KubaO/T-M-Reverse-Engineering/Power Designs 3240/PD3240.cir

[Main]
FileType=CIR
Version=12.00
Program=Micro-Cap
Component Version=10.00
Shape Version=11.00
Screen=1707,960
MCAPVersion=12.2.0.5
Key ID=Demo
NLCnt=299
TXCnt=4

[shapedef]
Name=Animated Meter
Animated Meter=0,-16,128,96
BColor=#000000
FColor=#E4E4E4
Current=-16,64,0,64

[shapedef]
Name=Bjt.root
Line=0,0,13,0
Rectangle=13,-12,15,12
Current=32,-24,32,-16
Current=32,24,32,16
Current=0,-8,8,-8
PolyOpen=3
PolyLine=24,-24
PolyLine=24,-12
PolyLine=14,-2
PolyOpen=3
PolyLine=24,24
PolyLine=24,12
PolyLine=14,2

[shapedef]
Name=Capacitor
Line=0,0,22,0
Line=22,-8,22,8
Line=26,-8,26,8
Line=26,0,48,0
Current=32,12,16,12

[shapedef]
Name=Diode
Root="Diode.root",0,0,0

[shapedef]
Name=Diode.root
Line=0,0,20,0
Line=28,0,48,0
Rectangle=18,-8,20,8
PolyClosed=3
PolyLine=20,0
PolyLine=28,-8
PolyLine=28,8
Current=32,16,16,16

[shapedef]
Name=Ground
Line=0,0,12,0
Line=12,-8,12,8
Line=18,-4,18,4
Line=24,0,24,0

[shapedef]
Name=NPN
Root="Bjt.root",0,0,0
PolyClosed=3
PolyLine=20,12
PolyLine=24,12
PolyLine=24,8

[shapedef]
Name=Plus.root
Line=-2,0,2,0
Line=0,-2,0,2

[shapedef]
Name=PNP
Root="Bjt.root",0,0,0
PolyClosed=3
PolyLine=17,-5
PolyLine=21,-5
PolyLine=17,-9
Line=16,-4,14,-2
Line=16,4,14,2

[shapedef]
Name=Pot
Line=0,0,12,0
Line=12,0,14,-4
Line=14,-4,18,4
Line=18,4,22,-4
Line=22,-4,26,4
Line=26,4,30,-4
Line=30,-4,34,4
Line=34,4,36,0
Line=36,0,48,0
PolyClosed=4
PolyLine=24,4
PolyLine=24,4
PolyLine=22,8
PolyLine=26,8
Line=24,8,24,16

[shapedef]
Name=Resistor
PolyOpen=12
PolyLine=0,0
PolyLine=0,0
PolyLine=12,0
PolyLine=14,-4
PolyLine=18,4
PolyLine=22,-4
PolyLine=26,4
PolyLine=30,-4
PolyLine=34,4
PolyLine=36,0
PolyLine=48,0
PolyLine=48,0
Current=32,8,16,8

[shapedef]
Name=SPICE_V
Root="Vsource.root",0,0,0

[shapedef]
Name=Vsource.root
Line=0,0,12,0
Line=36,0,48,0
Ellipse=12,-12,36,12
FColor=None
Line=7,5,7,9
Root="Plus.root",41,7,0
Current=32,16,16,16

[compdef]
Name=Voltage Source
Definition=VSpice
Shape=SPICE_V
Mask=5377
Used=73
memo=Voltage Source
Label Offset=19,13,15,13
PinCnt=2
Pin="Plus",6,0,-5,-6
Pin="Minus",0,0,-20,-6

[compdef]
Name=Resistor
Definition=Resistor
Shape=Resistor
Mask=7937
Used=267
memo=Resistor
Label Offset=18,6,8,11
PinCnt=2
Pin="Plus",6,0,-10,-4
Pin="Minus",0,0,-14,-4

[compdef]
Name=Capacitor
Definition=Capacitor
Shape=Capacitor
Mask=7425
Used=35
memo=Capacitor
Label Offset=16,12,12,12
PinCnt=2
Pin="Plus",6,0,-3,-5
Pin="Minus",0,0,-14,-5

[compdef]
Name=PNP
Definition=PNP
Shape=PNP
Mask=4097
Used=40
memo=PNP Transistor
Label Offset=37,-13,-8,35
PinCnt=3
Pin="Collector",3,3,6,3
Pin="Base",0,0,-19,-3
Pin="Emitter",3,-3,6,15

[compdef]
Name=Diode
Definition=Diode
Shape=Diode
Mask=4097
Used=51
memo=Diode
Label Offset=17,10,12,12
PinCnt=2
Pin="Anode",6,0,-9,-8
Pin="Cathode",0,0,-20,-8

[compdef]
Name=Pot
Definition=Macro
Shape=Pot
Mask=4864
Used=3
memo=Potentiometer Macro
Label Offset=32,4,9,11
PinCnt=3
Pin="PINA",a,0,0,-13,-5
Pin="PINB",a,3,2,6,5
Pin="PINC",a,6,0,-12,-5

[compdef]
Name=NPN
Definition=NPN
Shape=NPN
Mask=4097
Used=34
memo=NPN Transistor
Label Offset=37,-17,-14,33
PinCnt=3
Pin="Collector",3,-3,4,14
Pin="Base",0,0,-18,-3
Pin="Emitter",3,3,5,1

[compdef]
Name=Ground
Definition=Ground
Shape=Ground
Mask=1793
Used=311
memo=Ground
Label Offset=0,0,0,0
PinCnt=1
Pin="PinA",0,0,-3,-7

[compdef]
Name=Animated Meter
Definition=ANIMATED METER
Shape=Animated Meter
Mask=4096
Used=4
memo=Animated Digital/Analog Volt/Amp Meter
Label Offset=68,98,19,51
PinCnt=2
Pin="Plus",0,9,-24,4
Pin="Minus",0,11,-30,6

[Circuit]
Window Placement=2,3, -1,-1, -8,-31, 208,196,1419,708
Default Object=Color=#000080
Default Object Font=Height=-15,FStyle=0,Color=#000080,Name=Arial
Default Object Apply Border To Text=No
Default Object Apply Fill To Text=No
Default Object GridSnap=No
NodeVoltageFormat=3
CurrentFormat=3
PowerFormat=3
PathDelayFormat=3
WarningFormat=3
GridTextFormulaFormat=3
Window Placement in DC Analysis=2,3, -1,-1, -8,-31, 130,130,1594,604
SpiceType=AMBIGUOUS
Title_Block_Border=None
Title_Block=False
Show Nodes=False
Show Voltages=True
Show Current=True
Show Power=False
Show Condition=True
Show Pin Connections=False
Show Connection Warnings=False
Show Cross=False
Show Attribute Text=True
Show Grid Text=True

[Comp]
Name=Voltage Source
Px=192,328
Rot=3

[Attr]
ON=-31,-27,PART
V=V1
Style=8192

[Attr]
ON=-165,-41,VALUE
V=DC 33 AC 1 0 
Style=8192

[Attr]
ON=0,0,PACKAGE
V

[Attr]
ON=0,0,SMOOTHING
V=N
Style=256

[Attr]
ON=0,0,Saved_PulseS
V=N
Style=256

[Attr]
ON=0,0,FRACTION
V=.2
Style=256

[Attr]
ON=0,0,Saved_PulseF
V=.2
Style=256

[Attr]
ON=0,0,Saved_Pulse
V=DC 0 AC 1 0 Pulse 0 5 100n 10n 10n 400n 1u
Style=256

[Attr]
ON=0,0,Saved_None
V=DC 33 AC 1 0 
Style=256

[Attr]
ON=0,0,Saved_Sin
V=DC 0 AC 1 0 Sin 0 40 60
Style=256

[Wire]
Pxs=192,328,192,368

[Wire]
Pxs=192,368,200,368

[Wire]
Pxs=192,240,192,280

[Wire]
Pxs=192,240,208,240

[Wire]
Pxs=208,240,568,240

[Comp]
Name=Resistor
Px=1600,320
Rot=5

[Attr]
ON=8,-25,PART
V=RL1
Style=8192

[Attr]
ON=8,-39,RESISTANCE
V=10k
Style=8192

[Attr]
ON=0,0,PACKAGE
V

[Wire]
Pxs=1600,240,1600,272

[Comp]
Name=Capacitor
Px=1464,320
Rot=5

[Attr]
ON=12,-26,PART
V=C304
Style=8192

[Attr]
ON=12,-40,CAPACITANCE
V=4700u
Style=8192

[Attr]
ON=12,-54,MODEL
V=C4700u

[Attr]
ON=0,0,PACKAGE
V

[Wire]
Pxs=1464,240,1464,272

[Wire]
Pxs=1464,240,1600,240

[Wire]
Pxs=1464,320,1464,352

[Wire]
Pxs=1464,352,1536,352

[Wire]
Pxs=1600,320,1600,352

[Comp]
Name=PNP
Px=1440,544
COff=8,1440,544,-50,12

[Attr]
ON=37,-13,PART
V=Q203
Style=8192

[Attr]
ON=37,1,MODEL
V=2N3791

[Attr]
ON=37,29,PACKAGE
V=TO-204AA

[Comp]
Name=Resistor
Px=1464,472
Rot=5

[Attr]
ON=8,-25,PART
V=R203
Style=8192

[Attr]
ON=8,-39,RESISTANCE
V=0.1
Style=8192

[Attr]
ON=0,0,PACKAGE
V

[Comp]
Name=Resistor
Px=1600,472
Rot=5

[Attr]
ON=8,-25,PART
V=R204
Style=8192

[Attr]
ON=8,-39,RESISTANCE
V=0.1
Style=8192

[Attr]
ON=0,0,PACKAGE
V

[Comp]
Name=PNP
Px=1576,544
COff=8,1576,544,-52,12

[Attr]
ON=37,-13,PART
V=Q204
Style=8192

[Attr]
ON=37,1,MODEL
V=2N3791

[Attr]
ON=37,29,PACKAGE
V=TO-204AA

[Wire]
Pxs=1536,544,1536,616

[Wire]
Pxs=1392,544,1392,616

[Wire]
Pxs=1392,616,1536,616

[Wire]
Pxs=1464,472,1464,520

[Wire]
Pxs=1464,384,1464,424

[Wire]
Pxs=1600,384,1600,424

[Wire]
Pxs=1600,472,1600,520

[Wire]
Pxs=1464,568,1464,664

[Wire]
Pxs=1464,664,1536,664

[Wire]
Pxs=1600,568,1600,664

[Wire]
Pxs=1464,384,1536,384

[Wire]
Pxs=1536,352,1536,384

[Wire]
Pxs=1536,352,1552,352

[Wire]
Pxs=1536,384,1600,384

[Wire]
Pxs=1536,544,1576,544

[Wire]
Pxs=1392,544,1440,544

[Comp]
Name=Resistor
Px=1392,480
Rot=5

[Attr]
ON=8,-25,PART
V=R206
Style=8192

[Attr]
ON=8,-39,RESISTANCE
V=1k
Style=8192

[Attr]
ON=0,0,PACKAGE
V

[Wire]
Pxs=1392,240,1392,432

[Wire]
Pxs=1392,240,1464,240

[Wire]
Pxs=1392,480,1392,544

[Comp]
Name=PNP
Px=1440,856

[Attr]
ON=37,-13,PART
V=Q201
Style=8192

[Attr]
ON=37,1,MODEL
V=2N3791

[Attr]
ON=37,29,PACKAGE
V=TO-204AA

[Comp]
Name=Resistor
Px=1464,784
Rot=5

[Attr]
ON=8,-25,PART
V=R201
Style=8192

[Attr]
ON=9,-39,RESISTANCE
V=0.1
Style=8192

[Attr]
ON=0,0,PACKAGE
V

[Comp]
Name=Resistor
Px=1600,784
Rot=5

[Attr]
ON=8,-25,PART
V=R202
Style=8192

[Attr]
ON=8,-39,RESISTANCE
V=0.1
Style=8192

[Attr]
ON=0,0,PACKAGE
V

[Comp]
Name=PNP
Px=1576,856

[Attr]
ON=37,-13,PART
V=Q202
Style=8192

[Attr]
ON=37,1,MODEL
V=2N3791

[Attr]
ON=37,29,PACKAGE
V=TO-204AA

[Wire]
Pxs=1536,856,1536,928

[Wire]
Pxs=1464,784,1464,832

[Wire]
Pxs=1464,696,1464,736

[Wire]
Pxs=1600,696,1600,736

[Wire]
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
V

[Wire]
Pxs=272,280,272,672

[Wire]
Pxs=272,280,296,280

[Wire]
Pxs=272,720,272,1304

[Wire]
Pxs=272,1304,424,1304

[Wire]
Pxs=784,632,936,632

[Wire]
Pxs=936,632,936,648

[Wire]
Pxs=936,520,936,528

[Wire]
Pxs=976,576,992,576

[Wire]
Pxs=976,576,976,784

[Wire]
Pxs=888,784,976,784

[Wire]
Pxs=888,552,888,560

[Wire]
Pxs=888,784,888,832

[Wire]
Pxs=736,528,784,528

[Comp]
Name=Diode
Px=888,616
Rot=5

[Attr]
ON=12,-26,PART
V=D11
Style=8192

[Attr]
ON=12,-40,MODEL
V=1N4002

[Attr]
ON=12,-68,PACKAGE
V=DO-41

[Wire]
Pxs=888,616,888,784

[Comp]
Name=Voltage Source
Px=488,1016
Rot=5

[Attr]
ON=15,-27,PART
V=V302
Style=8192

[Attr]
ON=15,-41,VALUE
V=DC 15 AC 1 0 

[Attr]
ON=0,0,PACKAGE
V

[Attr]
ON=0,0,Saved_None
V=DC 15 AC 1 0 
Style=256

[Wire]
Pxs=488,1016,488,1304

[Wire]
Pxs=488,1304,712,1304

[Wire]
Pxs=888,376,936,376

[Wire]
Pxs=784,328,936,328

[Wire]
Pxs=856,616,888,616

[Wire]
Pxs=856,560,856,616

[Wire]
Pxs=856,560,888,560

[Wire]
Pxs=888,560,888,568

[Wire]
Pxs=928,528,936,528

[Wire]
Pxs=936,528,936,632

[Comp]
Name=Diode
Px=936,224
Rot=5

[Attr]
ON=12,-26,PART
V=D12
Style=8192

[Attr]
ON=12,-40,MODEL
V=1N4002

[Attr]
ON=12,-68,PACKAGE
V=DO-41

[Wire]
Pxs=936,224,936,280

[Comp]
Name=Diode
Px=936,176
Rot=5

[Attr]
ON=12,-26,PART
V=D13
Style=8192

[Attr]
ON=12,-40,MODEL
V=1N4002

[Attr]
ON=12,-68,PACKAGE
V=DO-41

[Wire]
Pxs=1224,112,1224,256

[Wire]
Pxs=1016,112,1112,112

[Wire]
Pxs=936,112,1016,112

[Wire]
Pxs=936,112,936,128

[Wire]
Pxs=504,112,504,280

[Wire]
Pxs=504,112,936,112

[Wire]
Pxs=1160,112,1224,112

[Wire]
Pxs=888,448,936,448

[Wire]
Pxs=888,448,888,504

[Wire]
Pxs=936,448,936,472

[Node Offsets]
Section=0
;Node,Page,GridX,GridY,OffsetX,OffsetY
Offset=15,0,936,328,-51,1

[Grid Text]
Text="OUT-"
Px=1552,352
GridSnap=True
JustifyH=Left
JustifyV=Bottom
CBorder=None

[Grid Text]
Text="PWR+"
Px=208,240
GridSnap=True
JustifyH=Left
JustifyV=Bottom
CBorder=None

[Grid Text]
Text="PWR-"
Px=200,368
GridSnap=True
JustifyH=Left
JustifyV=Bottom
CBorder=None

[Grid Text]
Text="Dynamic DC"
Text="Temperature=27"
Text="Displaying DC Voltages, Currents, Conditions"
Text="PGT = Total power generated = [PGT]"
Text="PDT = Total power dissipated = [PDT]"
BannerDC=True
Px=16,117
Height=-15
Color=#800000
Font=Arial
GridSnap=False
JustifyH=Left
JustifyV=Bottom
Formula=True
CFill=#C0C0C0
CBorder=#000000

[Schematic]
CurrentSection 0=0
CurrentSection 1=0
CurrentSection 2=0
CurrentSection 3=0
Splitter.xs=0
Splitter.ys=0
TextQuad=4099
Scale=0.66666666666666663
GridUser=10
ShapeGroups="Main","Euro","Polarity","Main1","Main11","Electrolytic","GroundArrow","DeMorgan"
CalcRMS=False
CalcAVG=False
CalcPeak=False
CalcVoltage=True
DisplayMeasure=Last
ShareScales=True

[Tools]
Pos=Top
FILESAVEASOLD=No
BOM=No
FILEPCB=No
PROBE=Yes
SELECT=Yes
PAN=Yes
COMP=Yes
TEXT=Yes
WIRE=Yes
WIRED=Yes
BUS=Yes
GRAPHIC=Yes
FLOWCHART=Yes
LINE=No
ELLIPSE=No
RECT=No
DIAM=No
ARC=No
PIE=No
TRIANGLE=No
STAR=No
LEFTBRK=No
RIGHTBRK=No
BOTHBRK=No
META=Yes
PARALLELOGRAM=No
FC_PROCESS=No
FC_ALT_PROCESS=No
FC_DECISION=No
FC_DATA=No
FC_PREDEFPROCESS=No
FC_INTERNALSTORAGE=No
FC_DOCUMENT=No
FC_MULTIDOCUMENT=No
FC_TERMINATOR=No
FC_PREPARATION=No
FC_MANUALINPUT=No
FC_MANUALOPERATION=No
FC_CONNECTOR=No
FC_OFFPAGECONNECTOR=No
FC_PUNCHCARD=No
FC_PUNCHEDTAPE=No
FC_SUMMING_JUNCTION=No
FC_OR=No
FC_COLLATE=No
FC_SORT=No
FC_EXTRACT=No
FC_MERGE=No
FC_STORED_DATA=No
FC_DELAY=No
FC_SAS=No
FC_MAGNETIC_DISK=No
FC_DAS=No
FC_DISPLAY=No
SPREAD_SHEET=Yes
POLYCLOS=No
POLYOPEN=No
FLAG=Yes
INFO=Yes
HELP=Yes
HELP_SPICE=No
LINK=Yes
CHECK=Yes
REGION_ENABLE=Yes
TITLE_BLOCK=Yes
DIGTRC=No
DIGTRC2=No
BUILD_COMMAND=Yes
DIGALL=No
GRIDTEXT=Yes
COMPTEXT=Yes
NODE=Yes
MEASURED=Yes
NODEV=Yes
CURRENT=Yes
POWER=Yes
CONDITIN=Yes
PIN=Yes
CONNWARN=Yes
CROSS=No
GRID=Yes
BORDER=Yes
BORDERONE=Yes
TITLE=Yes
RUBBER=Yes
PROPERTY=Yes
STEP=Yes
MIRROR=Yes
ROTATE=Yes
FLIPY=Yes
FLIPX=Yes
CIR_MAKEMACRO=No
CLEARCUTWIRE=No
CLIPBOARDCIRPAGE2BMM=No
FINDCOMP=Yes
FIND=Yes
REPEAT=No
REPLACE=No
MODEL=Yes
CIR2CKT=No
ATTDISP=No
ENABLE=Yes
DISABLE=Yes
ENABLE_WITH=Yes
TOFRONT=Yes
TOBACK=Yes
SELNEXT=No
PAGEADD=No
PAGEADDTEXT=No
ADDSECTION=No
PAGEDEL=No
ZOOMIN=Yes
ZOOMOUT=Yes
AUTOSCALECIR=Yes
GOTOFLAG=No
UPLEVEL=Yes
COLOR=Yes
FONT=Yes
STYLE=Yes
DM_LAST=No
DM_RMS=No
DM_AVG=No
DM_PEAK=No
GRID_NONE=No
GRID_NORMAL=No
GRID_BOLD_5=No
GRID_BOLD_6=No
GRID_BOLD_USER=No
GRAPH_PAPER=No
SPLITCIRTEXTH=No
SPLITCIRTEXTV=No
SPACE_SPLITTERS_EVENLY=No
NORMALCIR=No
RENAMEDEFINE=No
RENAMECMP=No
ATTALIGN=No
RESETNODEPOS=No
FIT2STANDARD=No
NODESNAP=No
MOVETEXT=No
TEXTINC=No
TOGGLETEXT=No
TOGGLEMODE=No
TOLERANCE=No
ALIGNAB=No
ALIGNLEFT=No
ALIGNCENTER=No
ALIGNRIGHT=No
ALIGNTOP=No
ALIGNMIDDLES=No
ALIGNBOTTOM=No

[Section]
Index=0
Name="PD3240"
Type=Main
Enable=True
CurrentPage 0=0
CurrentPage 1=0
CurrentPage 2=0
CurrentPage 3=0
TabSize 0=425
TabSize 1=425
TabSize 2=425
TabSize 3=425

[Page]
Index=0
Section=0
Print=True
Enable=True
Name=Main
PrinterScale=1
Scale 0=1
Scale 1=1
Scale 2=1
SB 3=466,192
Scale 3=0.66666666666666663
Px=972,443
WinBackGround Color=#FFFFFF
Select Color=#FF0000
Anchor Color=#000000
Select Box Color=#000080
Grid Text Color=Height=-12,FStyle=0,Color=#0000FF,Name=Verdana
Grid Text RTF=False
Grid Text Angle=0
Grid Text GridSnap=True
Grid Text PinIt=False
Grid Text JustifyH=Left
Grid Text JustifyV=Bottom
Grid GradientColor2=None
Grid OutlineThickness=1
Grid OutlineColor=None
Component Color=#0000FF
Attribute Text=Height=-12,FStyle=0,Color=#008000,Name=Verdana
Wire Color=#008000
Bus Color=#008000
Pin Connection=Height=-10,FStyle=0,Color=#FF0000,Name=Arial
Pin Marker Color=#008000
Node Number=Height=-11,FStyle=0,Color=#FF00FF,Name=Arial
Node Voltage Color=Height=-11,FStyle=0,Color=#000000,Name=Arial
Dynamic AC Voltage Color=#E4E4E4
Text Banner Text=Height=-15,FStyle=0,Color=#800000,Name=Arial
Title Block Background=#C0C0C0
Current=Height=-11,FStyle=0,Color=#0000FF,Name=Arial
Power/Condition=Height=-11,FStyle=0,Color=#FF0000,Name=Arial
Digital Path Color=#FF0000
Title Block Border=#000000
Disabled	Color=#C0C0C0
Search Color=#FFFF00
Grid Color=#000000
Graph Paper=#E4E4E4
Digital 0 Color=#000000
Digital R Color=#FFFF00
Digital F Color=#FFFF00
Digital 1 Color=#FF0000
Digital X Color=#C0C0C0
Digital Z Color=#808080
Block Select Color=#51F998

[Page]
Index=1
Section=0
Type=Text
Print=False
Enable=True
Name=Text
Font=Height=-15,FStyle=0,Color=#000000,Name=Courier New
Comment Color=#008000
WinBackGround Color=#FFFFFF
Disabled	Color=#C0C0C0
KeyWord Color=#0000FF
Error	Color=#FF0000
Search Color=#FFFF00

[Page]
Index=2
Section=0
Type=Text
Print=False
Enable=True
Name=Models
Font=Height=-15,FStyle=0,Color=#000000,Name=Courier New
Comment Color=#008000
WinBackGround Color=#FFFFFF
Disabled	Color=#C0C0C0
KeyWord Color=#0000FF
Error	Color=#FF0000
Search Color=#FFFF00

[Page]
Index=3
Section=0
Type=Info
Print=False
Enable=True
Name=Info
Font=Height=-15,FStyle=0,Color=#000000,Name=Courier New
Comment Color=#008000
WinBackGround Color=#FFFFFF
Disabled	Color=#C0C0C0
KeyWord Color=#0000FF
Error	Color=#FF0000
Search Color=#FFFF00

[Text Area]
Section=0
Page=1

[Text Area]
Section=0
Page=2
Text=* Schematic File
Text=*
Text=* Syntax:
Text=* .MODEL <model name> [AKO:<reference model name>] <ModelType>
Text=* +([<parameter name>=<value>][LOT[/#][/GAUSS|/UNIFORM|/WCASE]=[<tol>[%]] |[-<low>%,<high>%]][DEV[/#][/GAUSS|/UNIFORM|/WCASE]=[<tol>[%]]...)
Text=* ModelType must be one of OPA,D,NPN,NMOS,NJF,PUL,SIN,TRN,CORE,GASFET,VSWITCH,ISWITCH,CAP,IND,RES,PNP,PMOS,PJF,DOUTPUT,DINPUT,UADC,UDAC,UGATE,UTGATE,UEFF,UGFF,UDLY,UPLD,UROM,URAM,UBGT,UIO,LPNP,NIGBT,I,V
Text=*
Text=*Examples:
Text=* .MODEL 2N2222A NPN(BF=150 IS=1E-14)
Text=* .model M1 NMOS(KP=2.5E-5 VTO=1.345 CGDO=14.67p CGBO=4.566p)
Text=* .MODEL DK D(IS=1E-18)
Text=* .model 2N2222A AKO:2N2222 NPN (BF=55 ISE=10F)
Text=* .Model BJT1 NPN (RE=12 LOT/1/GAUSS=30% DEV/2/UNIFORM=2%)
Text=*
Text=* A .cir file is typically found in the data directory
Text=*
Text=*** From file C:\MC12\library\DIODE.LIB
Text=.MODEL MUR440 D (BV=400 CJO=64.37P IS=4.287U M=680.686M N=2.866 RL=1G
Text=+ RS=24.642M TT=123.315N VJ=1.353)
Text=.MODEL C8000U CAP (LS=5u RS=0.1)
Text=.MODEL C4700U CAP (LS=10u RS=0.2)

[InfoPage]
InfoPage=True
Warnings=True
System=True
Defines=True
Array=True
Model=True
Measure=True
MacroSubckt=True
NotUsed=True
ComponentCounts=True
VariablizePaths=False
DontShowPaths=False
SimulationLog=True
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
