KubaO/T-M-Reverse-Engineering/Kepco MPS620M/A1.kicad_sch

## KiCad design Kepco MPS620M/A1.kicad_sch (2022-07-01)

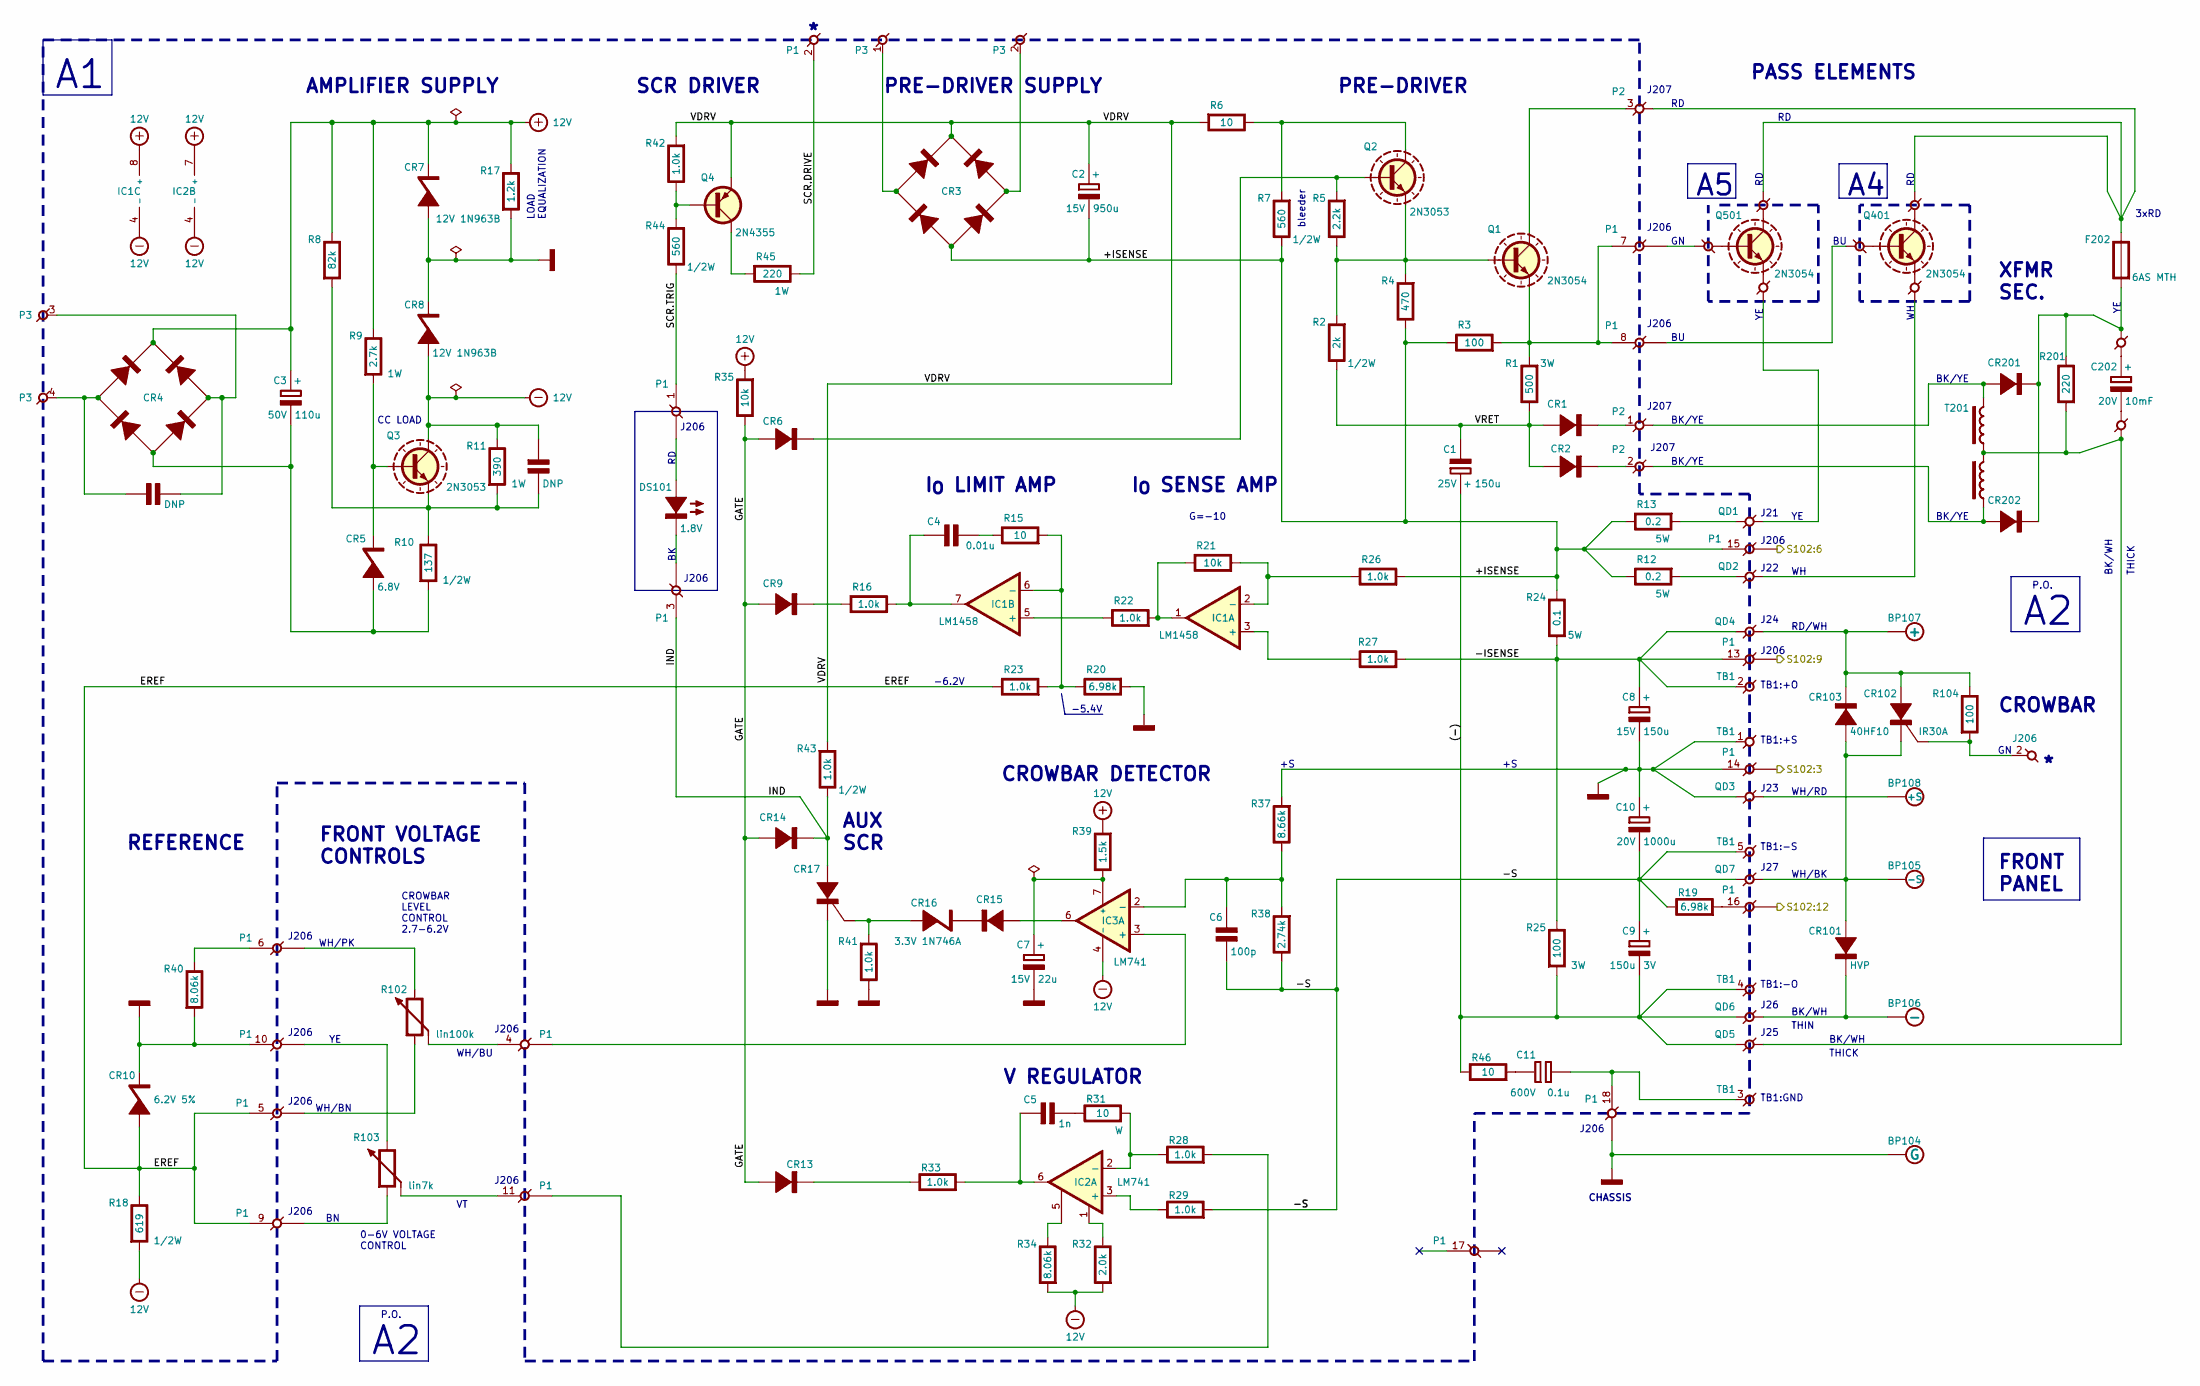
[picture p7: schematic A1.kicad_sch]

Parts:
BP104, BP105, BP106, BP107, BP108: K-socket-1
C1: 150u; Rating 25V
C2: 950u; Rating 15V
C3: 110u; Rating 50V
C4: 0.01u; Rating 200V
C5: 1n; Rating 200V
C6: 100p; Rating 500V
C7: 22u; Rating 15V
C8: 150u; Rating 15V
C9: 150u; Rating 3V
C10: 1000u; Rating 20V
C11: 0.1u; Rating 600V
C202: 10mF; Rating 20V
CR1, CR2: DR; Rating 100V, 1.5A
CR3, CR3_1, CR3_2, CR3_3, CR4, CR4_1, CR4_2, CR4_3: D-45; Rating V/A
CR5: 6.8V; Rating 0.5W
CR6, CR9, CR13, CR14, CR15: DSW; Rating 75V, 0.4W
CR7, CR8: 12V 1N963B; Rating 10mA
CR10: 6.2V 5%; Rating 7.5mA
CR16: 3.3V 1N746A; Rating 0.4W
CR17: S2061Y; Rating V/A
CR101: HVP; Rating V/A
CR102: IR30A; Rating V/A
CR103: 40HF10; Rating V/A
CR201, CR202: R2010; Rating 100V, 16A
CX1, CX2: DNP; Rating V
DS101: 1.8V; Rating A
F202: 6AS MTH; Rating W
IC1: LM1458
IC2, IC3: LM741
J1, J2, J3, J4, J5, J6, J7, J8: J-terminal
J206: J206
P1: P1
P2: P2
P3: P3
Q1, Q401, Q501: 2N3054
Q2, Q3: 2N3053
Q4: 2N4355
QD1, QD2, QD3, QD4, QD5, QD6, QD7: J-terminal
R1: 500; Rating 3W
R2: 2k; Rating 1/2W
R3, R104: 100; Rating W
R4: 470; Rating W
R5: 2.2k; Rating W
R6, R15, R31, R46: 10; Rating W
R7, R44: 560; Rating 1/2W
R8: 82k; Rating 1/2W
R9: 2.7k; Rating 1W
R10: 137; Rating 1/2W
R11: 390; Rating 1W
R12, R13: 0.2; Rating 5W
R16, R22, R23, R26, R27, R28, R29, R33, R41, R42: 1.0k; Rating W
R17: 1.2k; Rating 1/2W
R18: 619; Rating 1/2W
R19, R20: 6.98k; Rating W
R21, R35: 10k; Rating W
R24: 0.1; Rating 5W
R25: 100; Rating 3W
R32: 2.0k; Rating W
R34, R40: 8.06k; Rating W
R37: 8.66k; Rating W
R38: 2.74k; Rating W
R39: 1.5k; Rating W
R43: 1.0k; Rating 1/2W
R45: 220; Rating 1W
R102: 10k
R103: 7.0k
R201: 220; Rating 2W
T201, T201_2: L; Rating A
TB1: TB1

Connections:
(-): C1.1 (+), C9.2 (-), QD5.1, QD6.1, R25.2 (-), R46.1 (+), TB1.4
+ISENSE: C2.2 (-), CR3_2.2 (A+), CR3_3.2 (A+), P1.15, R3.1 (+), R4.1 (+), R7.1 (+), R12.1 (+), R13.1 (+), R24.1 (+), R26.2 (-)
-ISENSE: C8.1 (+), P1.13, QD4.1, R24.2 (-), R25.1 (+), R27.2 (-), TB1.2
-S: C6.1 (+), C9.1 (+), C10.2 (-), QD7.1, R19.1 (+), R29.2 (-), R38.1 (+), TB1.5
EREF: CR10.2 (A+), P1.5, P1.9, R18.1 (+), R23.1 (+)
GATE: CR6.2 (A+), CR9.2 (A+), CR13.2 (A+), CR14.2 (A+), R35.1 (+)
IND: CR14.1 (K-), CR17.2 (A+), P1.3, R43.1 (+)
unnamed: C3.2 (-), CR4_2.2 (A+), CR4_3.2 (A+), CR5.2 (A+), R10.2 (-)
unnamed: C4.1 (+), IC1.7 (OUTB), R16.2 (-)
unnamed: C4.2 (-), R15.1 (+)
unnamed: C5.1 (+), IC2.6 (OUT), R33.2 (-)
unnamed: C5.2 (-), R31.1 (+)
unnamed: C6.2 (-), IC3.2 (-), R37.1 (+), R38.2 (-)
unnamed: C7.1 (+), IC3.7 (+), R39.1 (+)
unnamed: C11.1 (+), R46.2 (-)
unnamed: C11.2 (-), P1.18, TB1.3
unnamed: C202.1 (+), J7.1
unnamed: C202.2 (-), J8.2
unnamed: CR1.1 (K-), P2.1
unnamed: CR2.1 (K-), P2.2
unnamed: CR3.2 (A+), CR3_3.1 (K-), P3.1
unnamed: CR3_1.2 (A+), CR3_2.1 (K-), P3.2
unnamed: CR4.2 (A+), CR4_3.1 (K-), CX1.1 (+), P3.4
unnamed: CR4_1.2 (A+), CR4_2.1 (K-), CX1.2 (-), P3.3
unnamed: CR5.1 (K-), Q3.2 (B), R9.2 (-)
unnamed: CR6.1 (K-), Q2.2 (B), R5.2 (-)
unnamed: CR9.1 (K-), R16.1 (+)
unnamed: CR13.1 (K-), R33.1 (+)
unnamed: CR15.1 (K-), CR16.1 (K-)
unnamed: CR15.2 (A+), IC3.6 (OUT)
unnamed: CR16.2 (A+), CR17.3 (G), R41.2 (-)
unnamed: CR101.1 (K-), QD6.2
unnamed: CR101.2 (A+), CR102.1 (K-), CR103.2 (A+), QD7.2
unnamed: CR102.2 (A+), CR103.1 (K-), QD4.2, R104.1 (+)
unnamed: CR102.3 (G), J206.2, R104.2 (-)
unnamed: CR201.1 (K-), CR202.1 (K-), F202.2 (-), J7.2, R201.1 (+)
unnamed: CR201.2 (A+), P2.1, T201.1 (+)
unnamed: CR202.2 (A+), P2.2, T201_2.2 (-)
unnamed: CX2.2 (-), Q3.3 (E), R8.2 (-), R10.1 (+), R11.2 (-)
unnamed: DS101.1 (K-), P1.3
unnamed: DS101.2 (A+), P1.1
unnamed: F202.1 (+), J2.2, J5.2, P2.3
unnamed: IC1.1 (OUTA), R21.1 (+), R22.2 (-)
unnamed: IC1.2 (-), R21.2 (-), R26.1 (+)
unnamed: IC1.3 (+), R27.1 (+)
unnamed: IC1.5 (+), R22.1 (+)
unnamed: IC1.6 (-), R15.2 (-), R20.1 (+), R23.2 (-)
unnamed: IC2.1 (OFSA), R32.1 (+)
unnamed: IC2.2 (-), R28.1 (+), R31.2 (-)
unnamed: IC2.3 (+), R29.1 (+)
unnamed: IC2.5 (OFSB), R34.1 (+)
unnamed: IC3.3 (+), P1.4
unnamed: J1.1, P1.7
unnamed: J1.2, Q501.2 (B)
unnamed: J2.1, Q501.1 (C)
unnamed: J3.1, QD1.1
unnamed: J3.2, Q501.3 (E)
unnamed: J4.1, P1.8
unnamed: J4.2, Q401.2 (B)
unnamed: J5.1, Q401.1 (C)
unnamed: J6.1, QD2.1
unnamed: J6.2, Q401.3 (E)
unnamed: J8.1, QD5.2, R201.2 (-), T201.2 (-), T201_2.1 (+)
unnamed: P1.4, R102.2 (b)
unnamed: P1.5, R102.1 (a)
unnamed: P1.6, R40.1 (+), R102.3 (c)
unnamed: P1.7, P1.8, Q1.3 (E), R1.2 (-), R3.2 (-)
unnamed: P1.9, R103.1 (a)
unnamed: P1.10, R103.3 (c)
unnamed: P1.11, R28.2 (-), R103.2 (b)
unnamed: P1.16, R19.2 (-)
unnamed: P2.3, Q1.1 (C)
unnamed: Q1.2 (B), Q2.3 (E), R2.2 (-), R4.2 (-), R5.1 (+)
unnamed: Q2.1 (C), R6.1 (+), R7.2 (-)
unnamed: Q4.1 (C), R45.2 (-)
unnamed: Q4.2 (B), R42.1 (+), R44.2 (-)
unnamed: QD1.2, R13.2 (-)
unnamed: QD2.2, R12.2 (-)
S102:3: P1.14
S102:6: P1.15
S102:9: P1.13
S102:12: P1.16
SCR.DRIVE: P1.2, R45.1 (+)
SCR.TRIG: P1.1, R44.1 (+)
V-+12: C3.1 (+), CR4.1 (K-), CR4_1.1 (K-), CR7.1 (K-), IC1.8 (+), IC2.7 (+), R8.1 (+), R9.1 (+), R17.1 (+), R35.2 (-), R39.2 (-)
V--12: CR8.2 (A+), CX2.1 (+), IC1.4 (-), IC2.4 (-), IC3.4 (-), Q3.1 (C), R11.1 (+), R18.2 (-), R32.2 (-), R34.2 (-)
V-GND: C7.2 (-), C8.2 (-), C10.1 (+), CR7.2 (A+), CR8.1 (K-), CR10.1 (K-), CR17.1 (K-), P1.10, P1.14, P1.18, QD3.1, R17.2 (-), R20.2 (-), R37.2 (-), R40.2 (-), R41.1 (+), TB1.1
VDRV: C2.1 (+), CR3.1 (K-), CR3_1.1 (K-), Q4.3 (E), R6.2 (-), R42.2 (-), R43.2 (-)
VRET: C1.2 (-), CR1.2 (A+), CR2.2 (A+), R1.1 (+), R2.1 (+)

Notes on the sheet:
AMPLIFIER SUPPLY
CROWBAR LEVEL CONTROL 2.7-6.2V
PRE-DRIVER
BK/YE
REFERENCE
J206
J207
CHASSIS
0-6V VOLTAGE CONTROL
WH/BK
WH/BN
J26
J22
P.O.
I_{O} LIMIT AMP
BK/WH THICK
TB1:-O
TB1:+O
J21
THIN
CROWBAR DETECTOR
CROWBAR
V REGULATOR
PRE-DRIVER SUPPLY
-6.2V
FRONT VOLTAGE CONTROLS
WH/BU
3xRD
J24
BK/WH
I_{O} SENSE AMP
J27
TB1:+S
THICK
J25
-5.4V
J23
TB1:GND
WH/PK
FRONT PANEL
CC LOAD
LOAD EQUALIZATION
G=-10
PASS ELEMENTS
TB1:-S
RD/WH
bleeder
AUX SCR
WH/RD
SCR DRIVER
XFMR SEC.
