KubaO/T-M-Reverse-Engineering/Kepco MPS620M/A3.kicad_sch

## KiCad design Kepco MPS620M/A3.kicad_sch (2022-07-01)

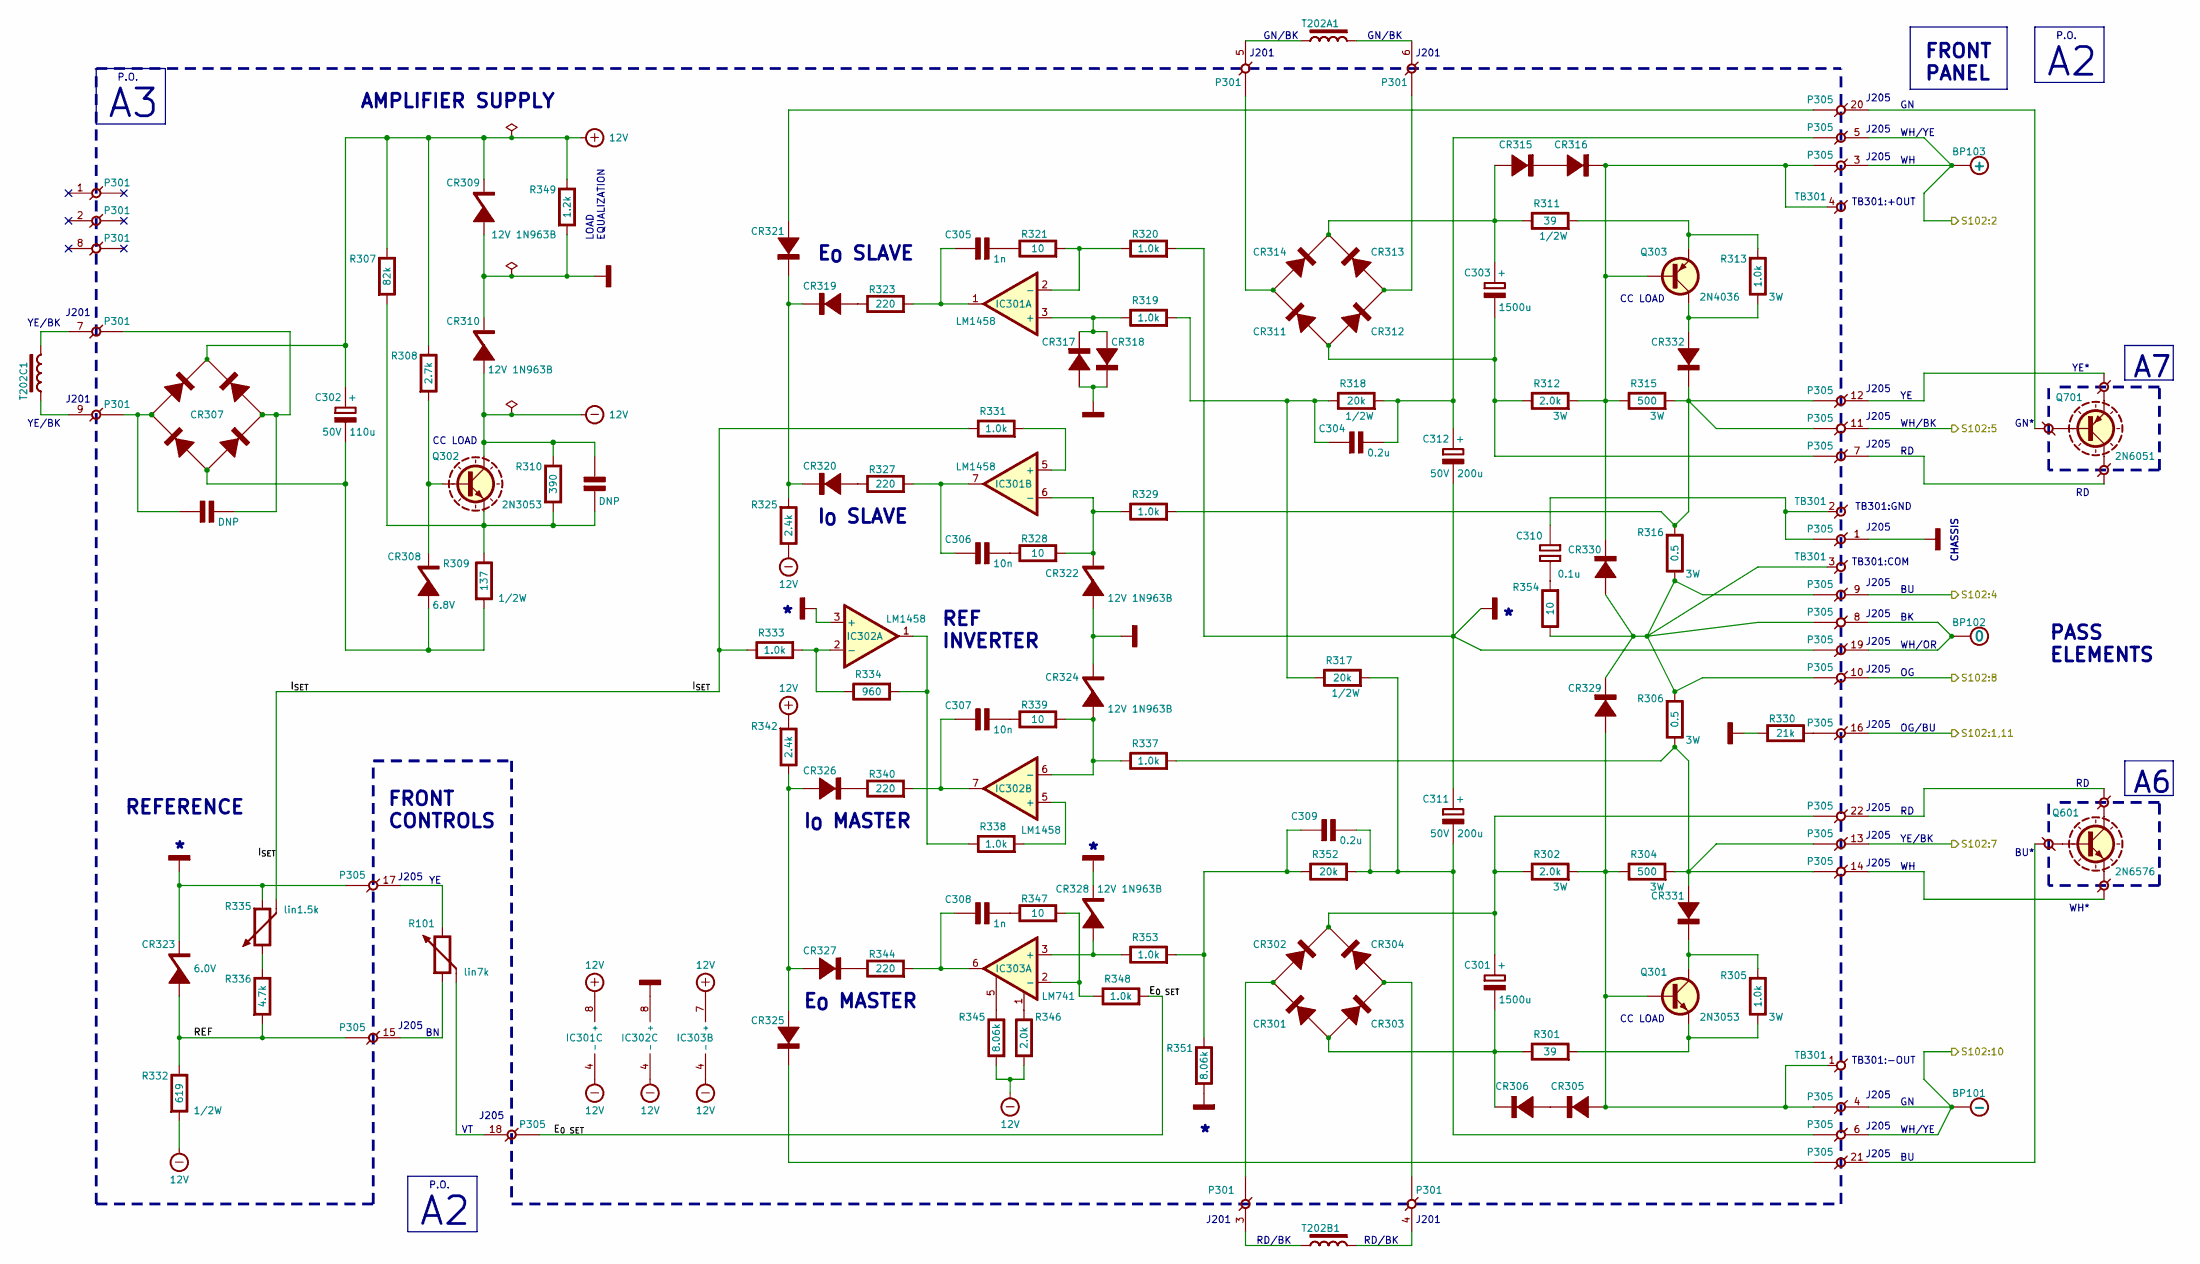
[picture p8: schematic A3.kicad_sch]

Parts:
BP101, BP102, BP103: K-socket-1
C301, C303: 1500u; Rating 75V
C302: 110u; Rating 50V
C304, C309: 0.2u; Rating 200V
C305, C308: 1n; Rating 200V
C306, C307: 10n; Rating 200V
C310: 0.1u; Rating 600V
C311, C312: 200u; Rating 50V
CR301, CR302, CR303, CR304, CR305, CR306, CR311, CR312, CR313, CR314, CR315, CR316, CR329, CR330: DR; Rating 100V, 1.5A
CR307, CR307_1, CR307_2, CR307_3: D-45; Rating V/A
CR308: 6.8V; Rating 0.5W
CR309, CR310, CR322, CR324, CR328: 12V 1N963B; Rating W
CR317, CR318, CR319, CR320, CR321, CR325, CR326, CR327, CR331, CR332: D; Rating V/A
CR323: 6.0V; Rating 7.5mA
CX301, CX302: DNP; Rating V
IC301, IC302: LM1458
IC303: LM741
J9, J10, J11, J12, J13, J14: J-terminal
P301: P301
P305: P305
Q301, Q302: 2N3053
Q303: 2N4036
Q601: 2N6576
Q701: 2N6051
R101: 7.0k
R301, R311: 39; Rating 1/2W
R302, R312: 2.0k; Rating 3W
R304, R315: 500; Rating 3W
R305, R313: 1.0k; Rating 3W
R306, R316: 0.5; Rating 3W
R307: 82k; Rating 1/2W
R308: 2.7k; Rating 1W
R309: 137; Rating 1/2W
R310: 390; Rating 1W
R317, R318, R352: 20k; Rating 1/2W
R319, R320, R329, R331, R333, R337, R338, R348, R353: 1.0k; Rating W
R321, R328, R339, R347, R354: 10; Rating W
R323, R327, R340, R344: 220; Rating W
R325, R342: 2.4k; Rating 1/2W
R330: 21k; Rating W
R332: 619; Rating 1/2W
R334: 960; Rating W
R335: 1.5k
R336: 4.7k; Rating 1/2W
R345, R351: 8.06k; Rating W
R346: 2.0k; Rating W
R349: 1.2k; Rating 1/2W
T202A1, T202B1, T202C1: L; Rating A
TB301: TB301

Connections:
E_{0 SET}: P305.18, R348.2 (-)
I_{SET}: R331.1 (+), R333.1 (+), R335.2 (b)
unnamed: C301.1 (+), CR302.1 (K-), CR304.1 (K-), P305.22, R302.1 (+)
unnamed: C301.2 (-), CR301.2 (A+), CR303.2 (A+), CR306.1 (K-), R301.1 (+)
unnamed: C302.2 (-), CR307_2.2 (A+), CR307_3.2 (A+), CR308.2 (A+), R309.2 (-)
unnamed: C303.1 (+), CR313.1 (K-), CR314.1 (K-), CR315.2 (A+), R311.1 (+)
unnamed: C303.2 (-), CR311.2 (A+), CR312.2 (A+), P305.7, R312.1 (+)
unnamed: C304.1 (+), R317.1 (+), R318.1 (+), R319.2 (-)
unnamed: C304.2 (-), C312.1 (+), P305.5, R318.2 (-)
unnamed: C305.1 (+), IC301.1 (OUTA), R323.2 (-)
unnamed: C305.2 (-), R321.1 (+)
unnamed: C306.1 (+), IC301.7 (OUTB), R327.2 (-)
unnamed: C306.2 (-), R328.1 (+)
unnamed: C307.1 (+), IC302.7 (OUTB), R340.2 (-)
unnamed: C307.2 (-), R339.1 (+)
unnamed: C308.1 (+), IC303.6 (OUT), R344.2 (-)
unnamed: C308.2 (-), R347.1 (+)
unnamed: C309.1 (+), R351.1 (+), R352.1 (+), R353.2 (-)
unnamed: C309.2 (-), C311.2 (-), P305.6, R317.2 (-), R352.2 (-)
unnamed: C310.1 (+), R354.2 (-)
unnamed: C310.2 (-), P305.1, TB301.2
unnamed: CR301.1 (K-), CR302.2 (A+), P301.3
unnamed: CR303.1 (K-), CR304.2 (A+), P301.4
unnamed: CR305.1 (K-), CR306.2 (A+)
unnamed: CR305.2 (A+), CR329.2 (A+), P305.4, Q301.2 (B), R302.2 (-), R304.1 (+), TB301.1
unnamed: CR307.2 (A+), CR307_3.1 (K-), CX301.1 (+), P301.9
unnamed: CR307_1.2 (A+), CR307_2.1 (K-), CX301.2 (-), P301.7
unnamed: CR308.1 (K-), Q302.2 (B), R308.2 (-)
unnamed: CR311.1 (K-), CR314.2 (A+), P301.5
unnamed: CR312.1 (K-), CR313.2 (A+), P301.6
unnamed: CR315.1 (K-), CR316.2 (A+)
unnamed: CR316.1 (K-), CR330.1 (K-), P305.3, Q303.2 (B), R312.2 (-), R315.1 (+), TB301.4
unnamed: CR317.1 (K-), CR318.2 (A+), IC301.3 (+), R319.1 (+)
unnamed: CR319.1 (K-), CR320.1 (K-), CR321.1 (K-), R325.2 (-)
unnamed: CR319.2 (A+), R323.1 (+)
unnamed: CR320.2 (A+), R327.1 (+)
unnamed: CR321.2 (A+), P305.20
unnamed: CR322.1 (K-), IC301.6 (-), R328.2 (-), R329.1 (+)
unnamed: CR324.2 (A+), IC302.6 (-), R337.1 (+), R339.2 (-)
unnamed: CR325.1 (K-), P305.21
unnamed: CR325.2 (A+), CR326.2 (A+), CR327.2 (A+), R342.1 (+)
unnamed: CR326.1 (K-), R340.1 (+)
unnamed: CR327.1 (K-), R344.1 (+)
unnamed: CR328.2 (A+), IC303.3 (+), R353.1 (+)
unnamed: CR329.1 (K-), CR330.2 (A+), P305.8, P305.9, P305.10, R306.2 (-), R316.1 (+), R354.1 (+), TB301.3
unnamed: CR331.1 (K-), Q301.1 (C), R305.2 (-)
unnamed: CR331.2 (A+), P305.13, P305.14, R304.2 (-), R306.1 (+), R337.2 (-)
unnamed: CR332.1 (K-), P305.11, P305.12, R315.2 (-), R316.2 (-), R329.2 (-)
unnamed: CR332.2 (A+), Q303.1 (C), R313.1 (+)
unnamed: CX302.2 (-), Q302.3 (E), R307.2 (-), R309.1 (+), R310.2 (-)
unnamed: IC301.2 (-), R320.1 (+), R321.2 (-)
unnamed: IC301.5 (+), R331.2 (-)
unnamed: IC302.1 (OUTA), R334.2 (-), R338.1 (+)
unnamed: IC302.2 (-), R333.2 (-), R334.1 (+)
unnamed: IC302.5 (+), R338.2 (-)
unnamed: IC303.1 (OFSA), R346.1 (+)
unnamed: IC303.2 (-), R347.2 (-), R348.1 (+)
unnamed: IC303.5 (OFSB), R345.1 (+)
unnamed: J9.1, P305.20
unnamed: J9.2, Q701.2 (B)
unnamed: J10.1, P305.21
unnamed: J10.2, Q601.2 (B)
unnamed: J11.1, Q701.3 (E)
unnamed: J11.2, P305.12
unnamed: J12.1, P305.7
unnamed: J12.2, Q701.1 (C)
unnamed: J13.1, Q601.1 (C)
unnamed: J13.2, P305.22
unnamed: J14.1, P305.14
unnamed: J14.2, Q601.3 (E)
unnamed: P301.3, T202B1.2 (-)
unnamed: P301.4, T202B1.1 (+)
unnamed: P301.5, T202A1.2 (-)
unnamed: P301.6, T202A1.1 (+)
unnamed: P301.7, T202C1.1 (+)
unnamed: P301.9, T202C1.2 (-)
unnamed: P305.15, R101.1 (a)
unnamed: P305.16, R330.2 (-)
unnamed: P305.17, R101.3 (c)
unnamed: P305.18, R101.2 (b)
unnamed: P305.8, P305.19
unnamed: Q301.3 (E), R301.2 (-), R305.1 (+)
unnamed: Q303.3 (E), R311.2 (-), R313.2 (-)
unnamed: R335.3 (c), R336.1 (+)
REF: CR323.2 (A+), P305.15, R332.1 (+), R336.2 (-)
S102:1,11: P305.16
S102:2: P305.3, P305.5
S102:4: P305.9
S102:5: P305.11
S102:7: P305.13
S102:8: P305.10
S102:10: P305.4, P305.6
V-+12: C302.1 (+), CR307.1 (K-), CR307_1.1 (K-), CR309.1 (K-), IC301.8 (+), IC303.7 (+), R307.1 (+), R308.1 (+), R342.2 (-), R349.1 (+)
V--12: CR310.2 (A+), CX302.1 (+), IC301.4 (-), IC302.4 (-), IC303.4 (-), Q302.1 (C), R310.1 (+), R325.1 (+), R332.2 (-), R345.2 (-), R346.2 (-)
V-GND: C311.1 (+), C312.2 (-), CR309.2 (A+), CR310.1 (K-), CR317.2 (A+), CR318.1 (K-), CR322.2 (A+), CR323.1 (K-), CR324.1 (K-), CR328.1 (K-), IC302.3 (+), IC302.8 (+), P305.1, P305.17, P305.19, R320.2 (-), R330.1 (+), R335.1 (a), R349.2 (-), R351.2 (-)

Notes on the sheet:
I_{O} SLAVE
J201
YE/BK
TB301:+OUT
J205
WH/YE
FRONT PANEL
RD/BK
TB301:GND
E_{O} SLAVE
CHASSIS
CC LOAD
OG/BU
TB301:COM
E_{O} MASTER
FRONT CONTROLS
LOAD EQUALIZATION
REFERENCE
I_{O} MASTER
YE*
GN/BK
WH/BK
PASS ELEMENTS
REF INVERTER
WH*
P.O.
BU*
WH/OR
TB301:-OUT
GN*
AMPLIFIER SUPPLY
