KubaO/T-M-Reverse-Engineering/Power Designs 3240/PD-3240.kicad_sch

## KiCad design Power Designs 3240/PD-3240.kicad_sch (2022-07-26)

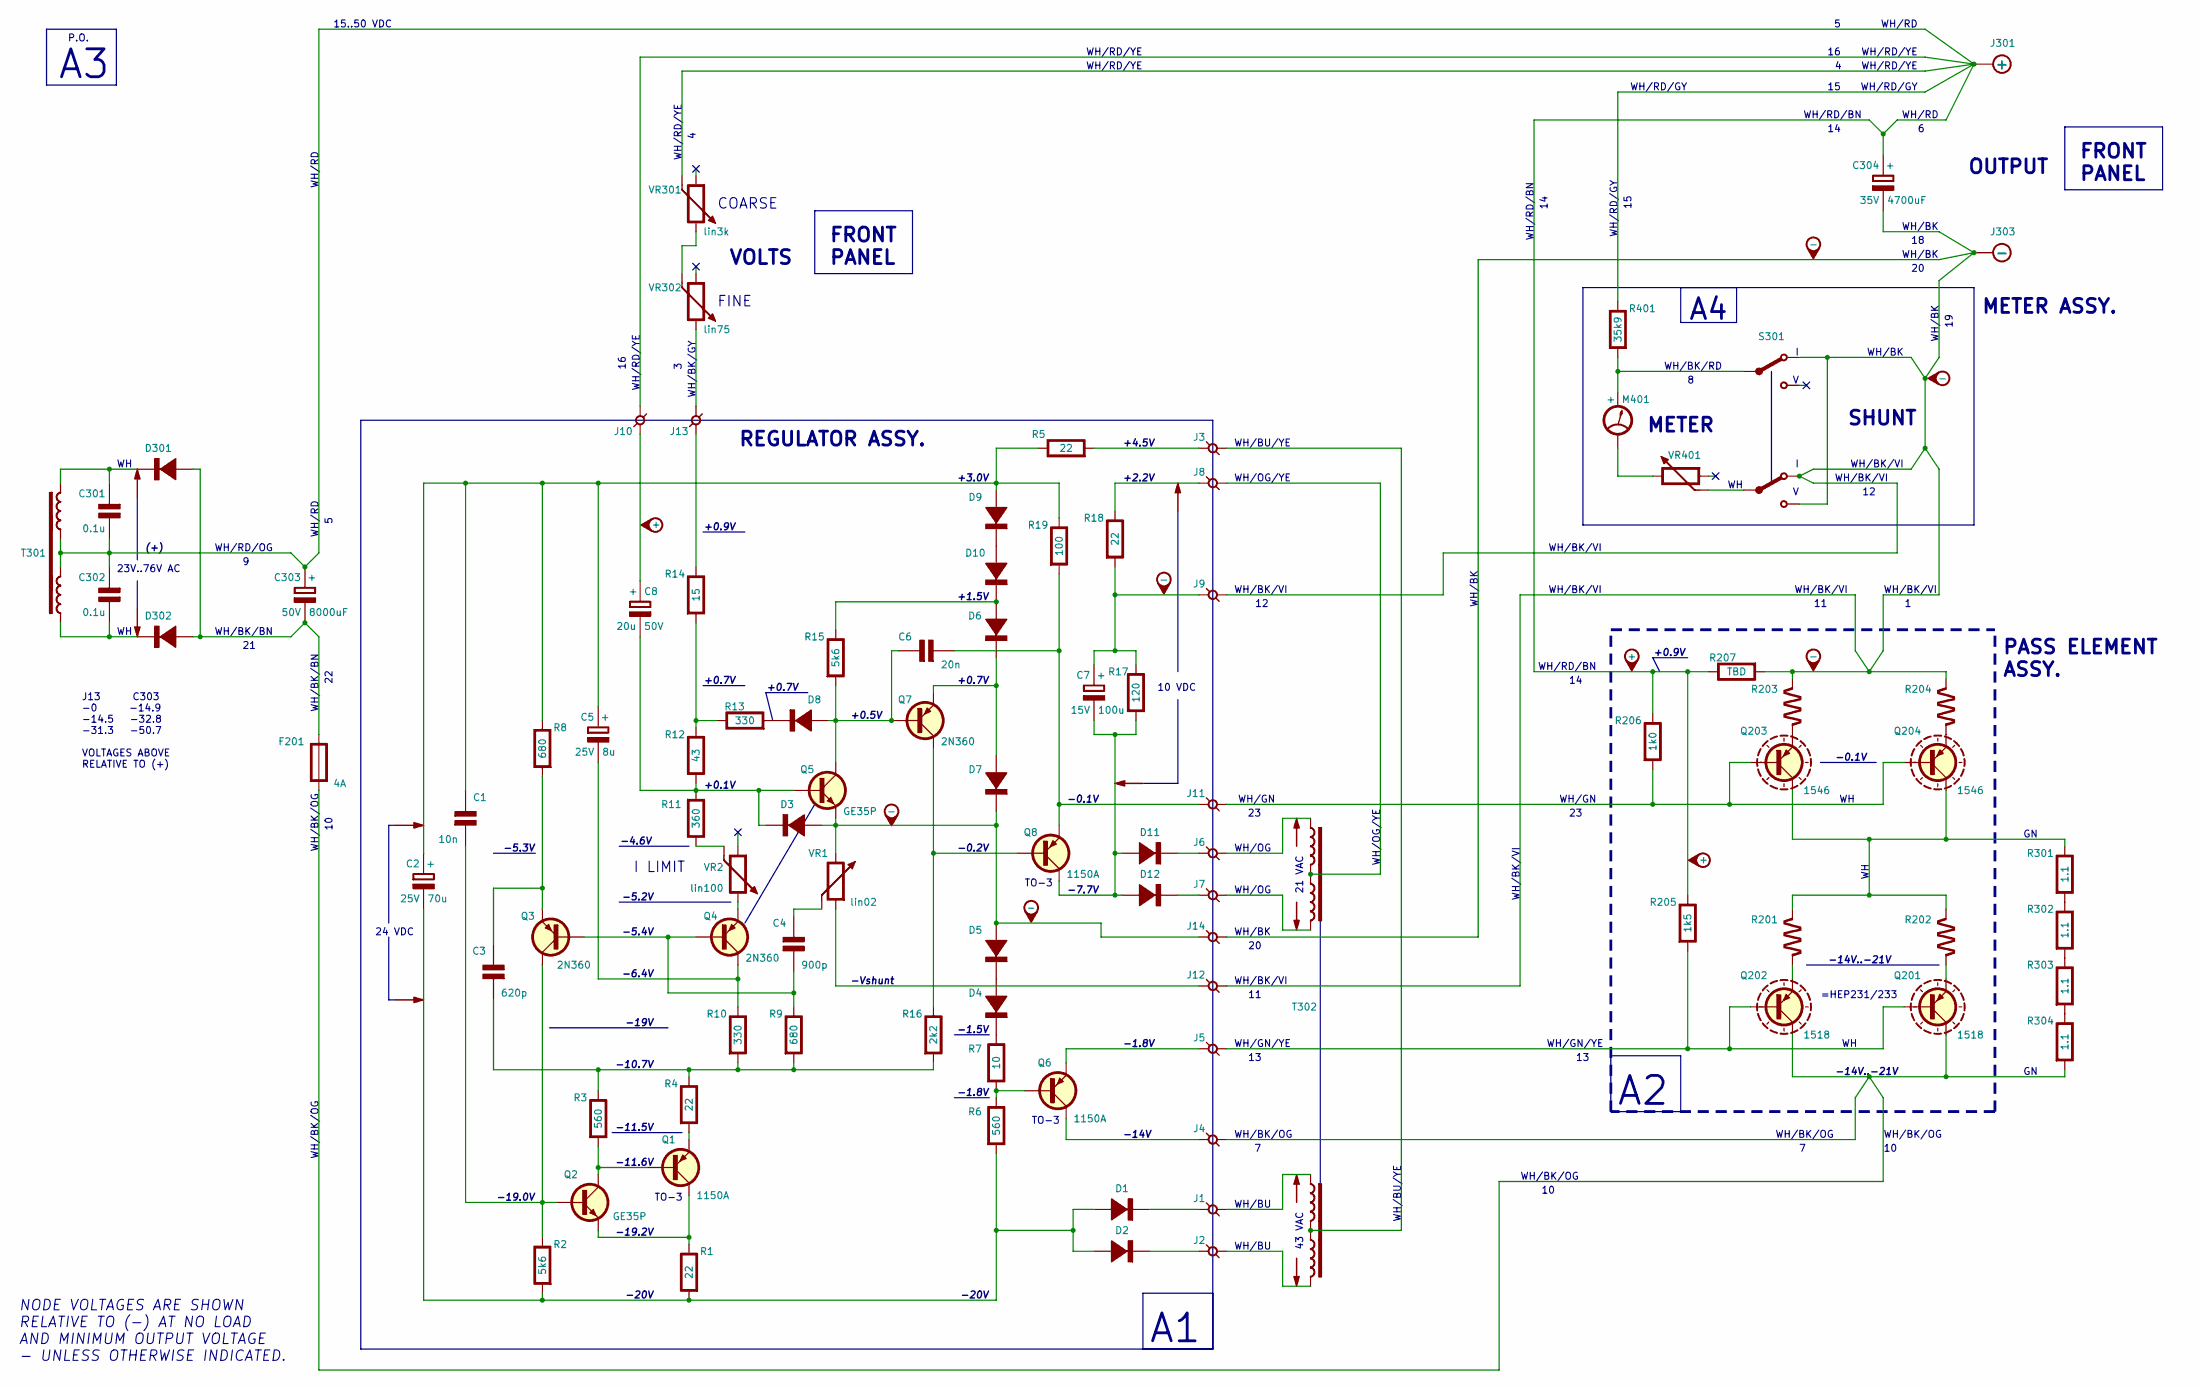
[picture p9: schematic PD-3240.kicad_sch]

Parts:
C1: 10n; Rating V
C2: 70u; Rating 25V
C3: 620p; Rating V
C4: 900p; Rating V
C5: 8u; Rating 25V
C6: 20n; Rating V
C7: 100u; Rating 15V
C8: 20u; Rating 50V
C301, C302: 0.1u; Rating V
C303: 8000uF; Rating 50V
C304: 4700uF; Rating 35V
D1, D2, D3, D4, D5, D6, D7, D8, D9, D10, D11, D12, D301, D302: D; Rating 100V, 16A
F201: 4A; Rating W
J1, J2, J3, J4, J5, J6, J7, J8, J9, J10, J11, J12, J13, J14: J-terminal
J301, J303: K-socket-1
M401: M-meter; Rating µA
Q1, Q6, Q8: 1150A
Q2, Q5: GE35P
Q3, Q4, Q7: 2N360
Q201, Q202: 1518
Q203, Q204: 1546
R1, R4, R5, R18: 22; Rating W
R2, R15: 5k6; Rating W
R3, R6: 560; Rating W
R7: 10; Rating W
R8, R9: 680; Rating W
R10, R13: 330; Rating W
R11: 360; Rating W
R12: 43; Rating W
R14: 15; Rating W
R16: 2k2; Rating W
R17: 120; Rating W
R19: 100; Rating W
R201, R202, R203, R204: 0.1; Rating W
R205: 1k5; Rating W
R206: 1k0; Rating W
R207: TBD; Rating W
R301, R302, R303, R304: 1.1; Rating W
R401: 35k9; Rating W
S301, S301_1: S-changeover; Rating V/A
T301, T301_2, T302, T302_2, T302_3, T302_4: L; Rating A
VR1, VR2, VR301, VR302, VR401: P

Connections:
unnamed: C1.1 (+), Q2.2 (B), Q3.1 (C), R2.1 (+)
unnamed: C1.2 (-), C2.1 (+), C5.1 (+), D9.2 (A+), R5.1 (+), R8.1 (+), R19.1 (+)
unnamed: C2.2 (-), D1.2 (A+), D2.2 (A+), R1.2 (-), R2.2 (-), R6.2 (-)
unnamed: C3.1 (+), R3.1 (+), R4.1 (+), R9.2 (-), R10.2 (-), R16.2 (-)
unnamed: C3.2 (-), Q3.3 (E), R8.2 (-)
unnamed: C4.1 (+), Q3.2 (B), Q4.2 (B), R9.1 (+)
unnamed: C4.2 (-), VR1.2 (b)
unnamed: C5.2 (-), Q4.1 (C), R10.1 (+)
unnamed: C6.1 (+), J11.1, Q8.3 (E), R19.2 (-)
unnamed: C6.2 (-), D8.2 (A+), Q5.1 (C), Q7.2 (B), R15.2 (-)
unnamed: C7.1 (+), J9.1, R17.1 (+), R18.2 (-)
unnamed: C7.2 (-), D11.2 (A+), D12.2 (A+), Q8.1 (C), R17.2 (-)
unnamed: C8.1 (+), J10.2
unnamed: C8.2 (-), D3.1 (K-), Q5.2 (B), R11.2 (-), R12.2 (-)
unnamed: C301.1 (+), D301.1 (K-), T301.1 (+)
unnamed: C301.2 (-), C302.1 (+), C303.1 (+), C304.1 (+), J10.1, R205.1 (+), R206.1 (+), R207.1 (+), R401.1 (+), T301.2 (-), T301_2.1 (+), VR301.2 (b)
unnamed: C302.2 (-), D302.1 (K-), T301_2.2 (-)
unnamed: C303.2 (-), D301.2 (A+), D302.2 (A+), F201.1 (+)
unnamed: C304.2 (-), J9.2, J12.2, J14.2, R203.1 (+), R204.1 (+), R207.2 (-), S301.2, S301_1.2, S301_1.4
unnamed: D1.1 (K-), J1.1
unnamed: D2.1 (K-), J2.1
unnamed: D3.2 (A+), D5.2 (A+), D7.1 (K-), J14.1, Q5.3 (E), VR1.3 (c)
unnamed: D4.1 (K-), R7.1 (+)
unnamed: D4.2 (A+), D5.1 (K-)
unnamed: D6.1 (K-), D7.2 (A+), Q7.3 (E)
unnamed: D8.1 (K-), R13.2 (-)
unnamed: D6.2 (A+), D10.1 (K-), R15.1 (+)
unnamed: D9.1 (K-), D10.2 (A+)
unnamed: D11.1 (K-), J6.1
unnamed: D12.1 (K-), J7.1
unnamed: F201.2 (-), J4.2, Q201.1 (C), Q202.1 (C), R304.2 (-)
unnamed: J1.2, T302_3.1 (+)
unnamed: J2.2, T302_4.2 (-)
unnamed: J3.1, R5.2 (-)
unnamed: J3.2, T302_3.2 (-), T302_4.1 (+)
unnamed: J4.1, Q6.1 (C)
unnamed: J5.1, Q6.3 (E)
unnamed: J5.2, Q201.2 (B), Q202.2 (B), R205.2 (-)
unnamed: J6.2, T302.1 (+)
unnamed: J7.2, T302_2.2 (-)
unnamed: J8.1, R18.1 (+)
unnamed: J8.2, T302.2 (-), T302_2.1 (+)
unnamed: J11.2, Q203.2 (B), Q204.2 (B), R206.2 (-)
unnamed: J12.1, VR1.1 (a)
unnamed: J13.1, VR302.3 (c)
unnamed: J13.2, R14.1 (+)
unnamed: M401.1 (+), R401.2 (-), S301.1
unnamed: M401.2 (-), VR401.3 (c)
unnamed: Q1.1 (C), Q2.3 (E), R1.1 (+)
unnamed: Q1.2 (B), Q2.1 (C), R3.2 (-)
unnamed: Q1.3 (E), R4.2 (-)
unnamed: Q4.3 (E), VR2.3 (c)
unnamed: Q6.2 (B), R6.1 (+), R7.2 (-)
unnamed: Q7.1 (C), Q8.2 (B), R16.1 (+)
unnamed: Q201.3 (E), R202.2 (-)
unnamed: Q202.3 (E), R201.2 (-)
unnamed: Q203.1 (C), Q204.1 (C), R201.1 (+), R202.1 (+), R301.1 (+)
unnamed: Q203.3 (E), R203.2 (-)
unnamed: Q204.3 (E), R204.2 (-)
unnamed: R11.1 (+), VR2.2 (b)
unnamed: R12.1 (+), R13.1 (+), R14.2 (-)
unnamed: R301.2 (-), R302.1 (+)
unnamed: R302.2 (-), R303.1 (+)
unnamed: R303.2 (-), R304.1 (+)
unnamed: S301_1.1, VR401.2 (b)
unnamed: VR301.3 (c), VR302.2 (b)

Notes on the sheet:
TO-3
WH/RD/OG
WH/BK/OG
-19.0V
VOLTS
WH/RD/YE
WH/BU/YE
WH/OG
-5.2V
-19V
WH/RD
-0.1V
COARSE
23V..76V AC
WH/BK/VI
(+)
-1.5V
FRONT PANEL
+0.9V
-5.3V
WH/BK/BN
43 VAC
-Vshunt
=HEP231/233
24 VDC
WH/BK
-14V
FINE
15..50 VDC
I LIMIT
-4.6V
WH/RD/GY
WH/BU
NODE VOLTAGES ARE SHOWN RELATIVE TO (-) AT NO LOAD AND MINIMUM OUTPUT VOLTAGE - UNLESS OTHERWISE INDICATED.
+0.1V
WH/RD/BN
-0.2V
-11.5V
WH/OG/YE
-14V..-21V
PASS ELEMENT ASSY.
-20V
-10.7V
+1.5V
10 VDC
-7.7V
+0.5V
WH/GN
-5.4V
+0.7V
+3.0V
WH/BK/GY
REGULATOR ASSY.
P.O.
+2.2V
J13 C303 -0 -14.9 -14.5 -32.8 -31.3 -50.7 VOLTAGES ABOVE RELATIVE TO (+)
-1.8V
WH/GN/YE
-11.6V
-6.4V
OUTPUT
METER ASSY.
WH/BK/RD
21 VAC
+4.5V
METER
SHUNT
-19.2V
